redruM0381/ATAboy/FW source/v.6f3/tusb_config.h

#ifndef _TUSB_CONFIG_H_
#define _TUSB_CONFIG_H_

#define CFG_TUSB_RHPORT0_MODE    OPT_MODE_DEVICE
#define CFG_TUD_CDC              1
#define CFG_TUD_MSC              1
#define CFG_TUD_MSC_EP_BUFSIZE   4096
#define CFG_TUD_CDC_RX_BUFSIZE   256
#define CFG_TUD_CDC_TX_BUFSIZE   512

#endif
